Nic-io/synesthete/src/ux/touch/touch.h

/*
 * Copyright (c) 2021 Nicolas Blazevic <nicolas@ecliptic.fr>
 *
 * SPDX-License-Identifier: Apache-2.0
 */
#ifndef __SYNESTHETE_TOUCH_H_
#define __SYNESTHETE_TOUCH_H_

#include "adc.h"
#include "gpio.h"

typedef struct xyPos {
	int x;
	int y;
	int rawy;
} xyPos;

void touch_init();
void touch_read();
xyPos touch_get();

#endif
