Nic-io/synesthete/src/adc/adc.c

/*
 * Copyright (c) 2020 Libre Solar Technologies GmbH
 *
 * SPDX-License-Identifier: Apache-2.0
 */

#include "adc.h"

LOG_MODULE_REGISTER(Synesthete_ADC, LOG_LEVEL_INF);

#if !DT_NODE_EXISTS(DT_PATH(zephyr_user)) || \
	!DT_NODE_HAS_PROP(DT_PATH(zephyr_user), io_channels)
#error "No suitable devicetree overlay specified"
#endif
#define ADC_NODE		DT_PHANDLE(DT_PATH(zephyr_user), io_channels)
/* Common settings supported by most ADCs */
#define ADC_RESOLUTION		12
#define ADC_GAIN		ADC_GAIN_1
#define ADC_REFERENCE		ADC_REF_INTERNAL
#define ADC_ACQUISITION_TIME	ADC_ACQ_TIME_DEFAULT

static int16_t sample_buffer;
static const struct device *dev_adc;

static struct adc_channel_cfg channel_cfg = {
	.gain = ADC_GAIN,
	.reference = ADC_REFERENCE,
	.acquisition_time = ADC_ACQUISITION_TIME,
	/* channel ID will be overwritten below */
	.channel_id = 1,
	.differential = 0
};

static struct adc_sequence sequence = {
	/* individual channels will be added below */
	.channels    = 0,
	.buffer      = &sample_buffer,
	/* buffer size in bytes, not number of samples */
	.buffer_size = sizeof(sample_buffer),
	.resolution  = ADC_RESOLUTION,
};

void adc_init(void){
	int32_t adc_vref;
	dev_adc = DEVICE_DT_GET(ADC_NODE);

	if (!device_is_ready(dev_adc)) {
		printk("ADC device not found\n");
		return;
	}
	adc_channel_setup(dev_adc, &channel_cfg);
	adc_vref = adc_ref_internal(dev_adc);
	LOG_DBG("ADC intenal ref voltage = %d", adc_vref);
}

int adc_get_touch_axis(touchAxis axis){

	channel_cfg.channel_id = axis;
	sequence.channels = BIT(axis);

	k_sleep(K_USEC(500));
	adc_channel_setup(dev_adc, &channel_cfg);
	int err = adc_read(dev_adc, &sequence);
	
	if (err != 0) {
		LOG_ERR("ADC reading failed with error %d.\n", err);
		return err;
	}
	return sample_buffer;
}
